Tomato-Masks/diy-fine-particulate-mask/designs/type-1/assets/CAD/misc/accordion-fold-diagram.png

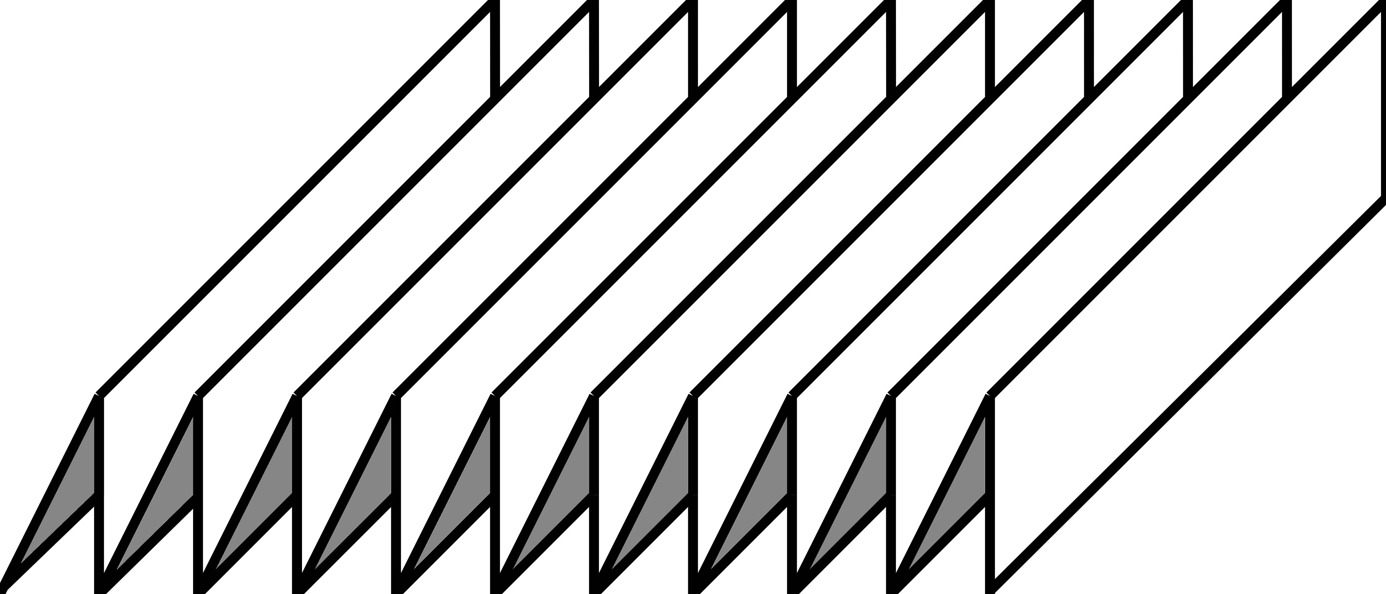
designs/type-1/assets/CAD/misc/accordion-fold-diagram.png
