Tomato-Masks/diy-fine-particulate-mask/designs/type-1/assets/CAD/misc/concept.png

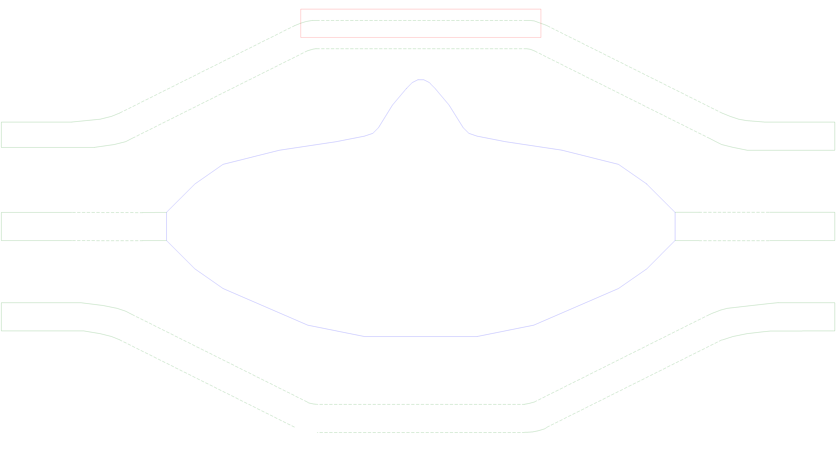
designs/type-1/assets/CAD/misc/concept.png
