Tomato-Masks/diy-fine-particulate-mask/designs/type-1/assets/images/inner-layer/design-sewed-edges-inner-layer-270by210.png

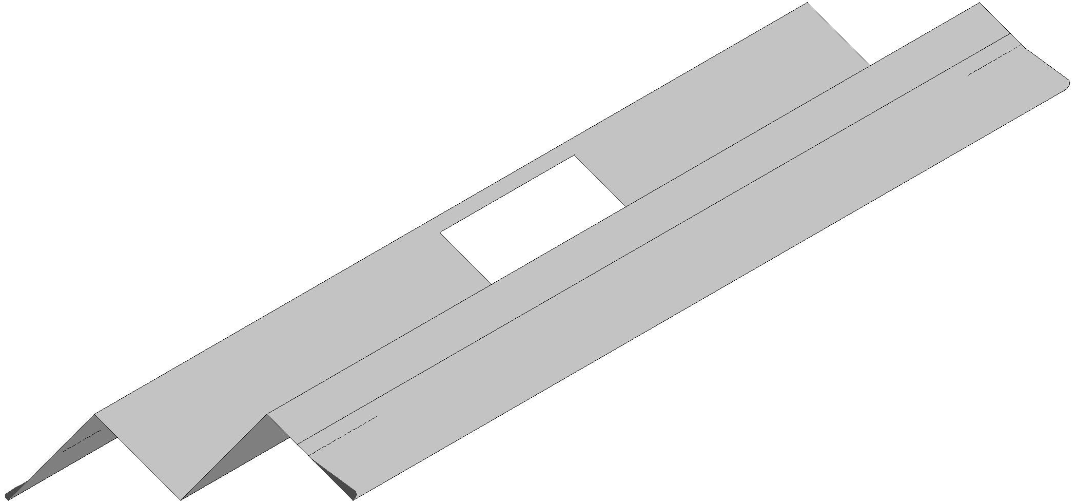
designs/type-1/assets/images/inner-layer/design-sewed-edges-inner-layer-270by210.png
