Tomato-Masks/diy-fine-particulate-mask/designs/type-1/assets/images/inner-layer/v04-inner-7.jpg

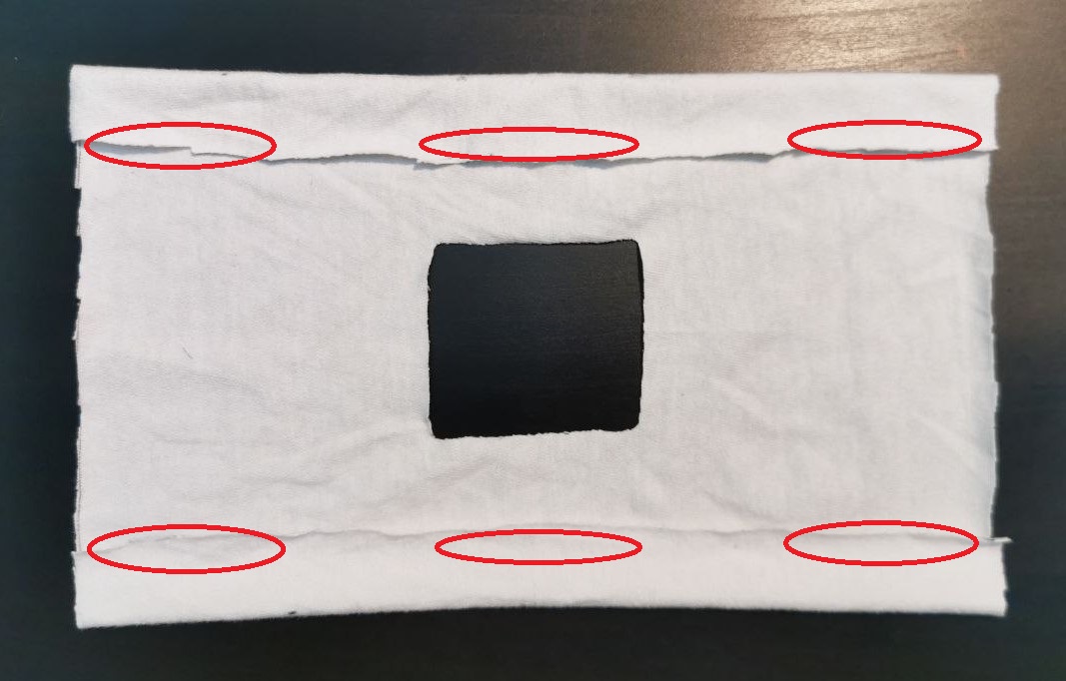
designs/type-1/assets/images/inner-layer/v04-inner-7.jpg
