Tomato-Masks/diy-fine-particulate-mask/designs/type-1/assets/images/misc/arch/inner-layer-labelled.png

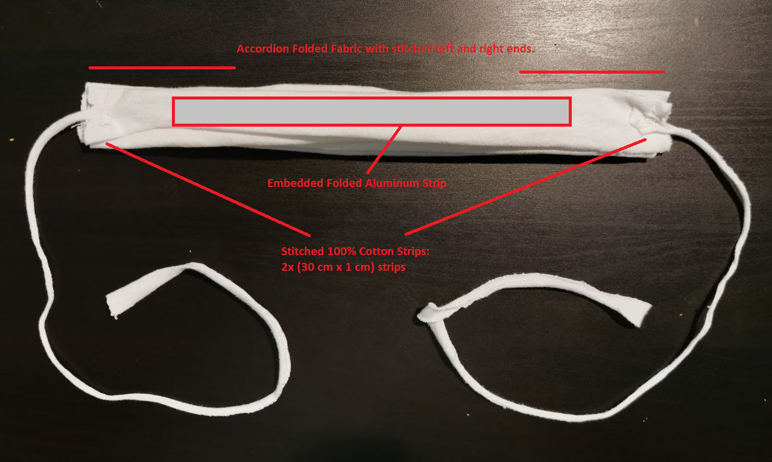
designs/type-1/assets/images/misc/arch/inner-layer-labelled.png
