Tomato-Masks/diy-fine-particulate-mask/designs/type-1/assets/images/misc/arch/inner-shell.jpg

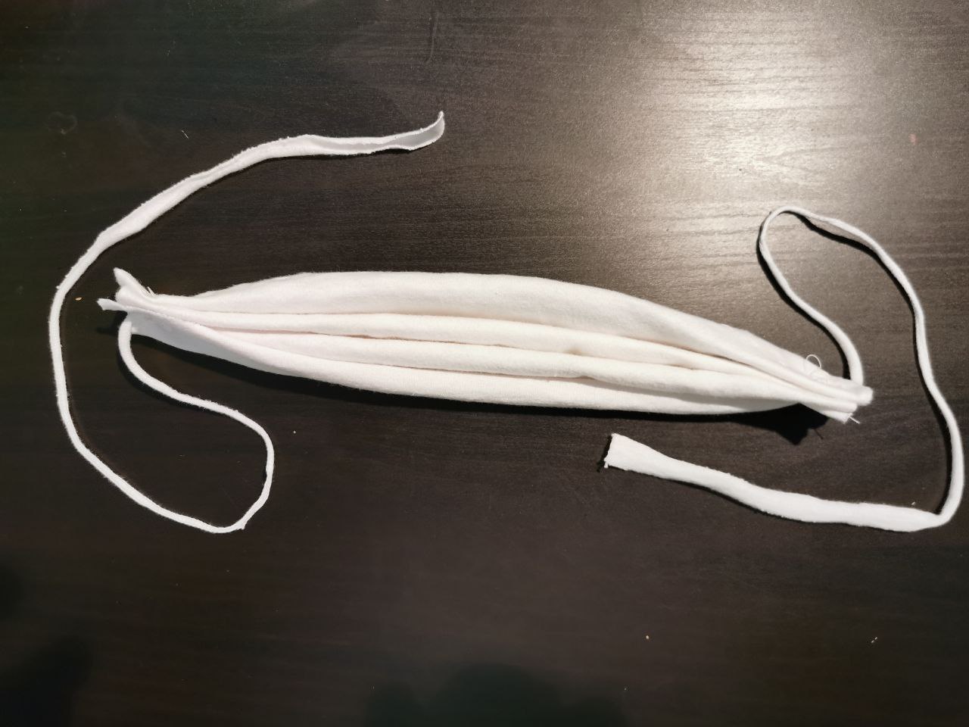
designs/type-1/assets/images/misc/arch/inner-shell.jpg
