Tomato-Masks/diy-fine-particulate-mask/designs/type-1/assets/images/misc/arch/rectangle.jpg

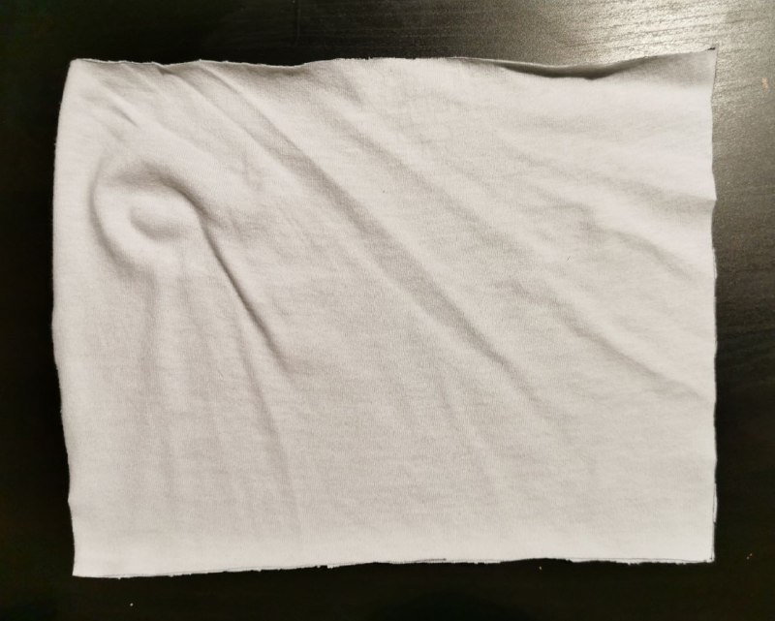
designs/type-1/assets/images/misc/arch/rectangle.jpg
