Tomato-Masks/diy-fine-particulate-mask/designs/type-1/assets/images/misc/arch/Small-Stencil-Outer-Layer.png

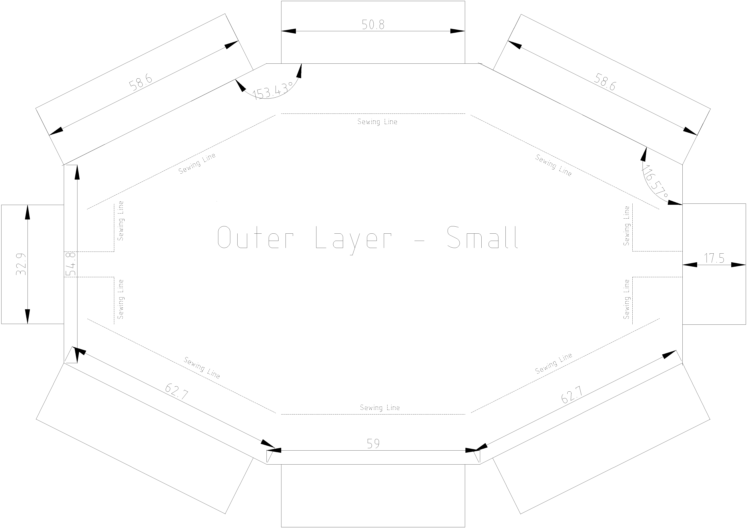
designs/type-1/assets/images/misc/arch/Small-Stencil-Outer-Layer.png
