Tomato-Masks/diy-fine-particulate-mask/designs/type-1/assets/images/misc/arch/v04-outer-layer.jpg

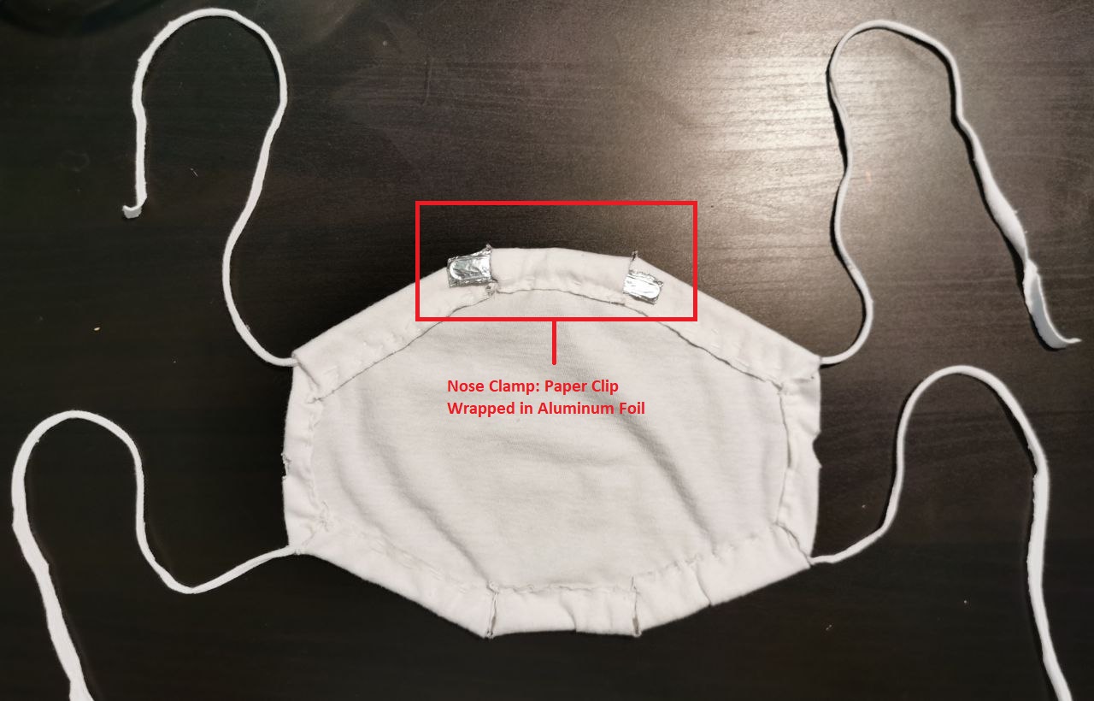
designs/type-1/assets/images/misc/arch/v04-outer-layer.jpg
