Tomato-Masks/diy-fine-particulate-mask/designs/type-1/assets/images/misc/inner-layer-fold.png

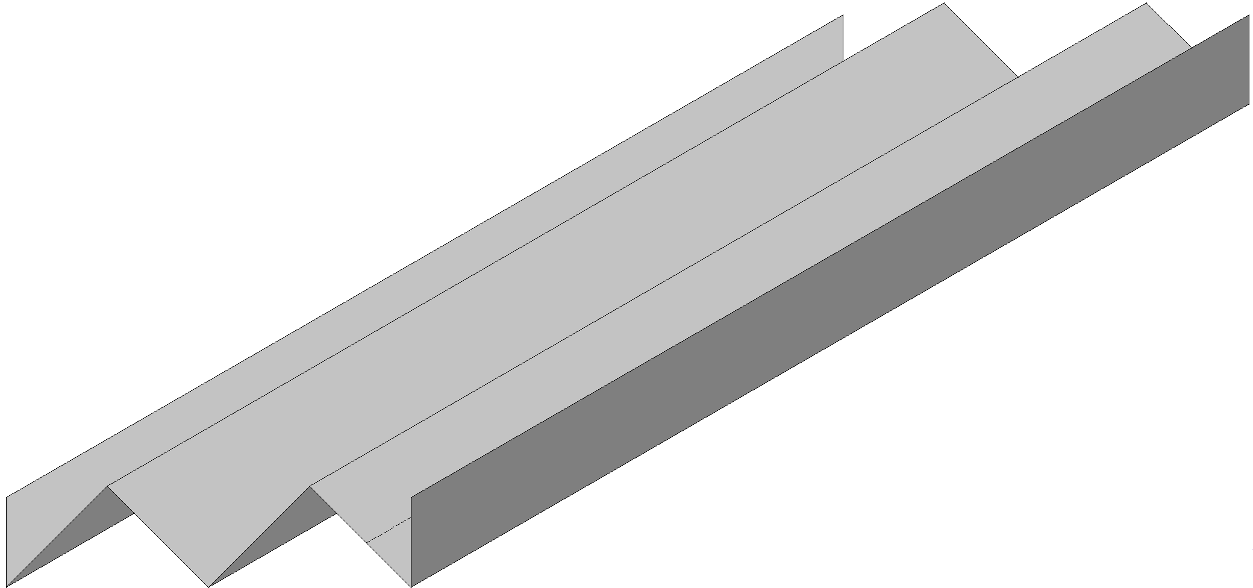
designs/type-1/assets/images/misc/inner-layer-fold.png
