Tomato-Masks/diy-fine-particulate-mask/designs/type-1/assets/images/misc/reference-inner-layer-270by210.png

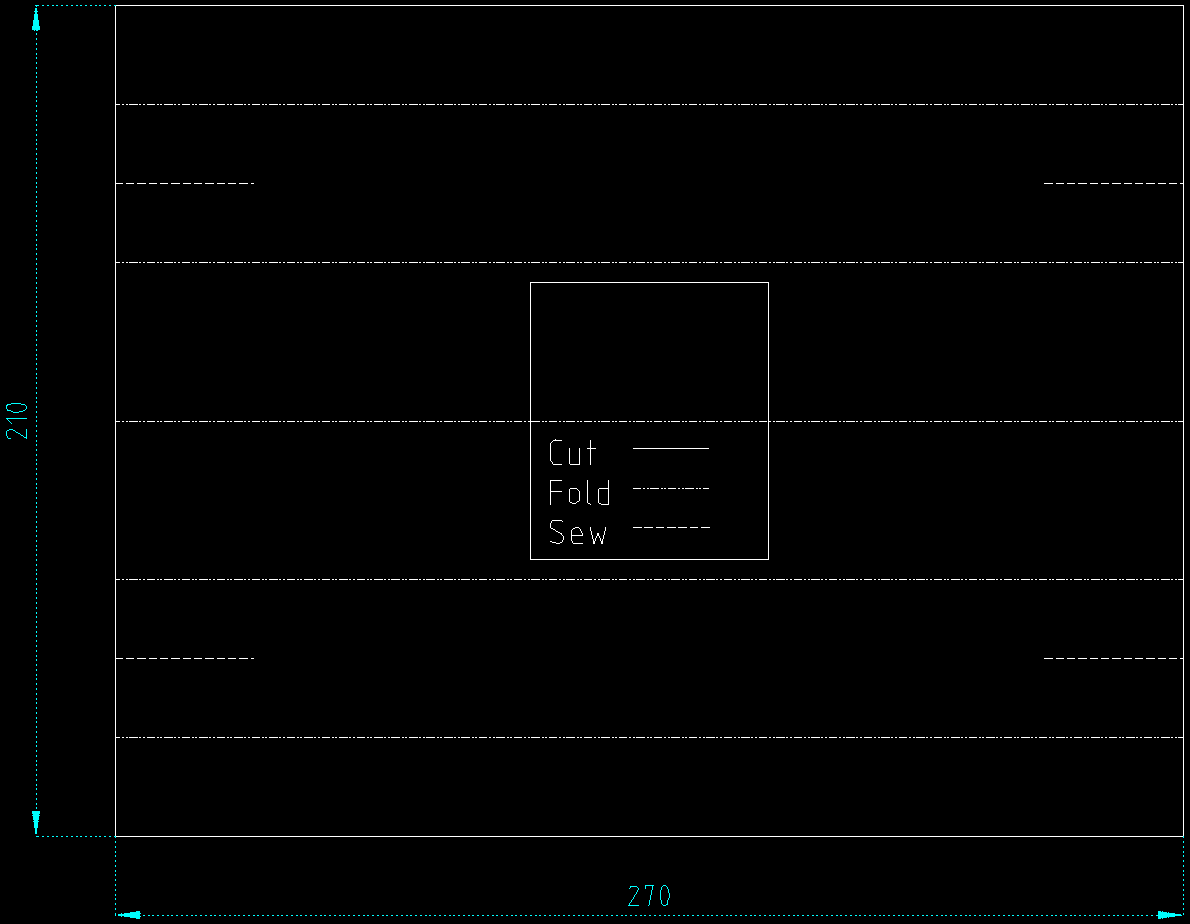
designs/type-1/assets/images/misc/reference-inner-layer-270by210.png
