Tomato-Masks/diy-fine-particulate-mask/designs/type-1/assets/images/misc/reference-outer-layer-270by200.png

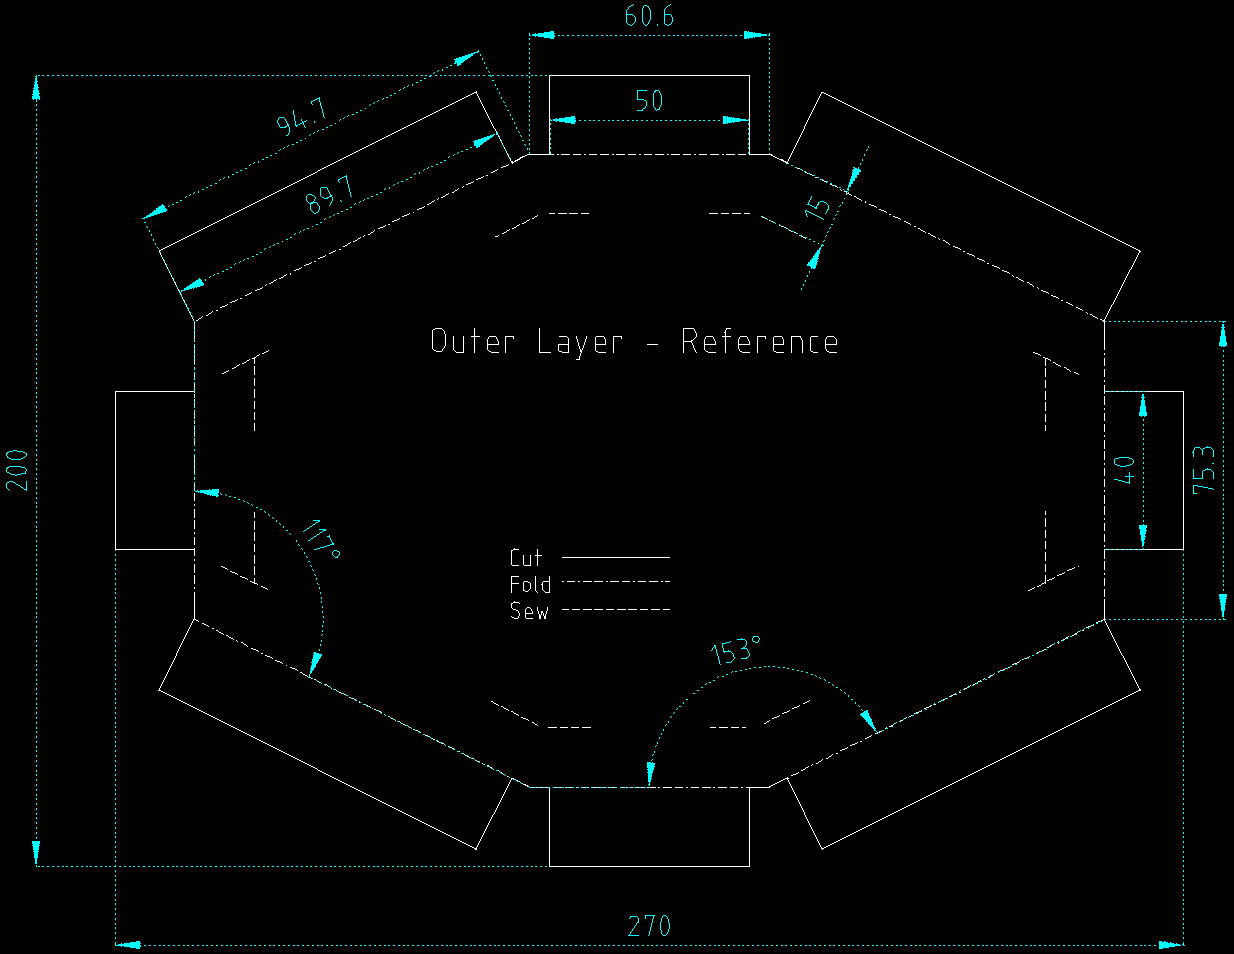
designs/type-1/assets/images/misc/reference-outer-layer-270by200.png
