Tomato-Masks/diy-fine-particulate-mask/designs/type-1/assets/images/misc/v04-inner-10.jpg

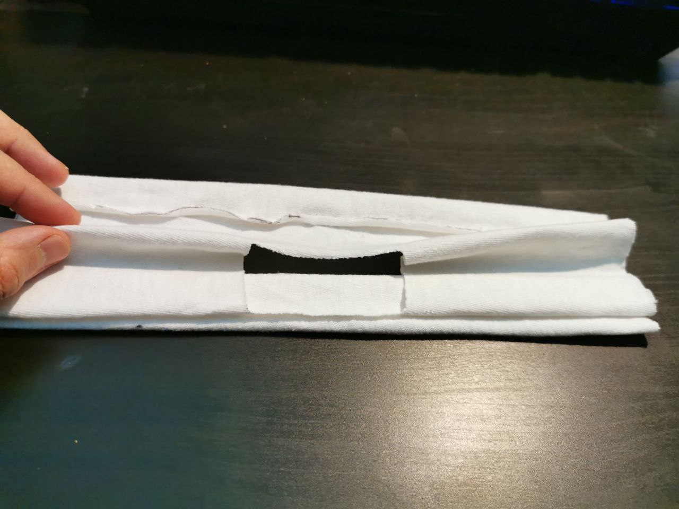
designs/type-1/assets/images/misc/v04-inner-10.jpg
