Tomato-Masks/diy-fine-particulate-mask/designs/type-1/assets/images/misc/v04-inner-12.jpg

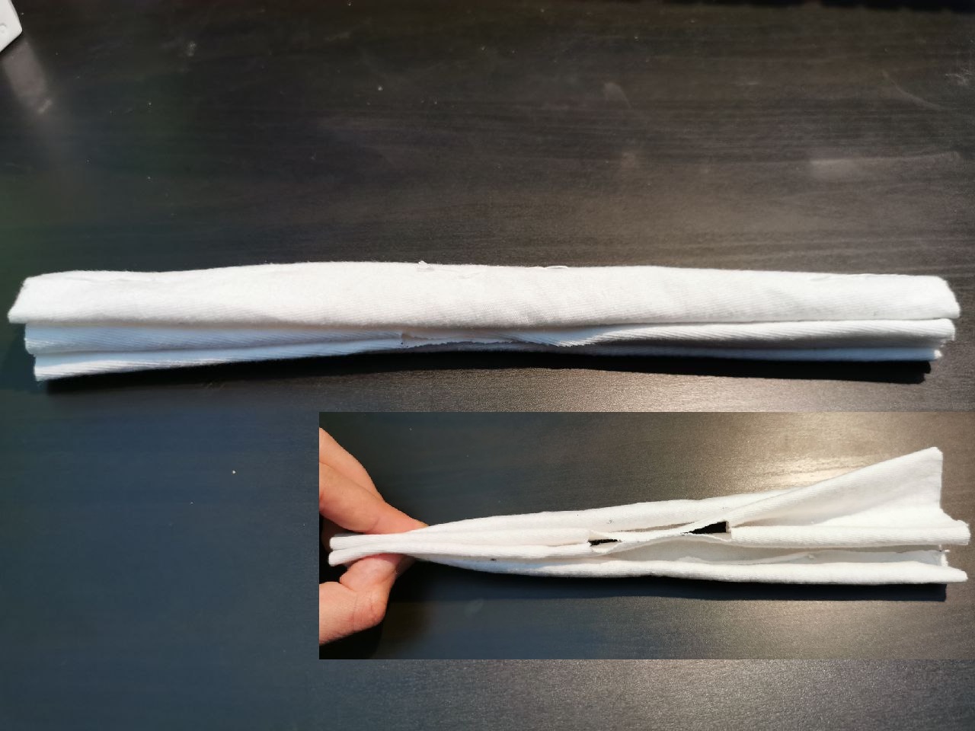
designs/type-1/assets/images/misc/v04-inner-12.jpg
