Tomato-Masks/diy-fine-particulate-mask/designs/type-1/assets/images/preparation/fabric-stripes.jpg

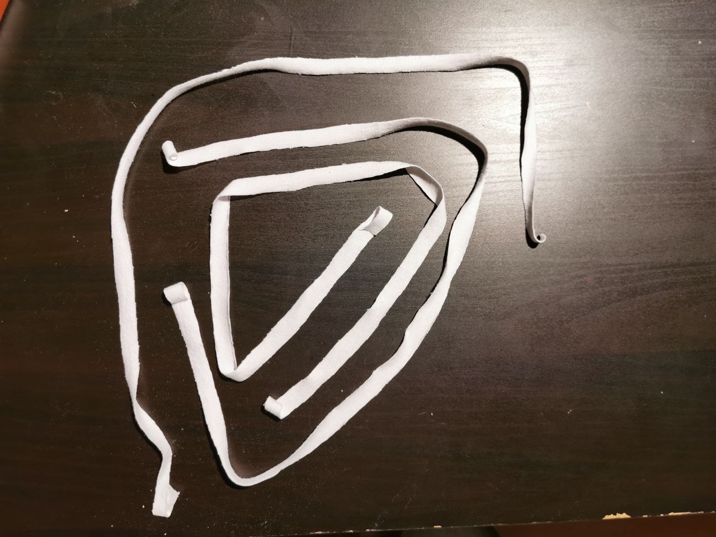
designs/type-1/assets/images/preparation/fabric-stripes.jpg
