Tomato-Masks/diy-fine-particulate-mask/designs/type-1/assets/images/preparation/roll-paper-stripe.jpg

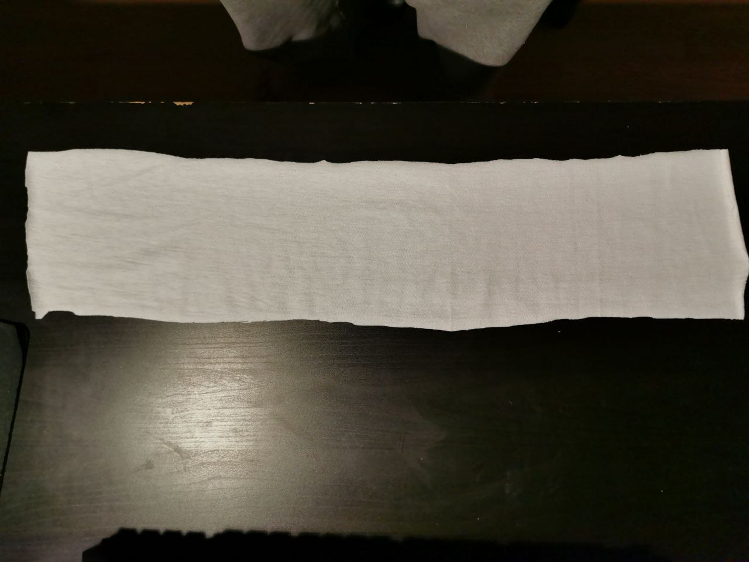
designs/type-1/assets/images/preparation/roll-paper-stripe.jpg
