Tomato-Masks/diy-fine-particulate-mask/designs/type-1/assets/images/preparation/stripe-roll.jpg

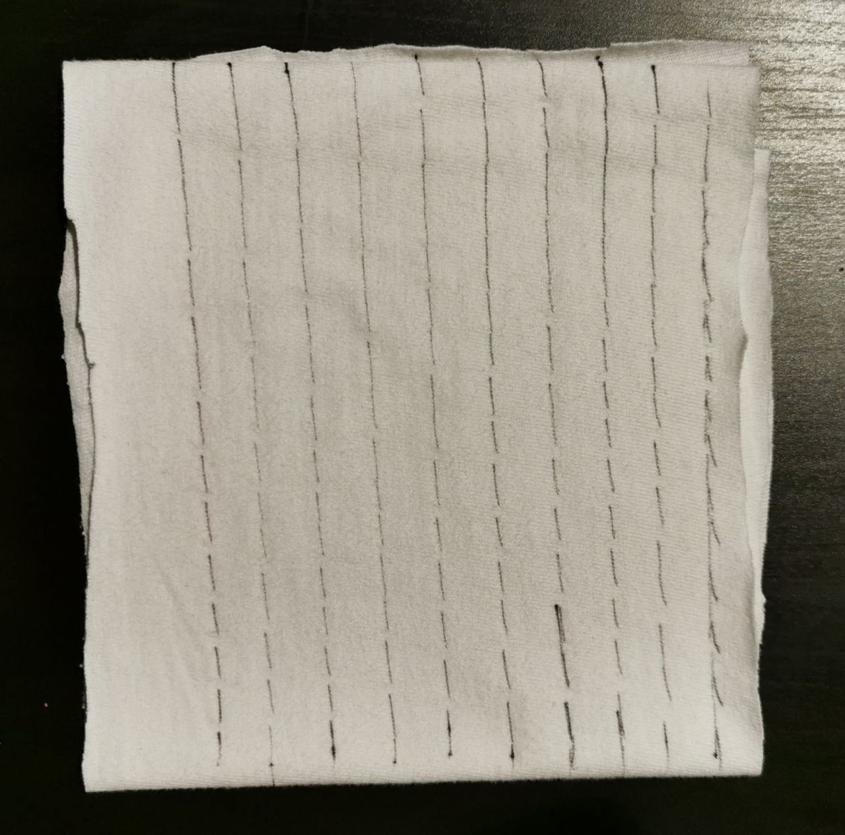
designs/type-1/assets/images/preparation/stripe-roll.jpg
