Tomato-Masks/diy-fine-particulate-mask/designs/type-1/assets/images/type1v04/fitting-v04-2b.jpg

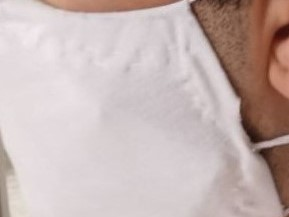
designs/type-1/assets/images/type1v04/fitting-v04-2b.jpg
