Tomato-Masks/diy-fine-particulate-mask/designs/type-1/assets/images/type1v04/v04-12b.jpg

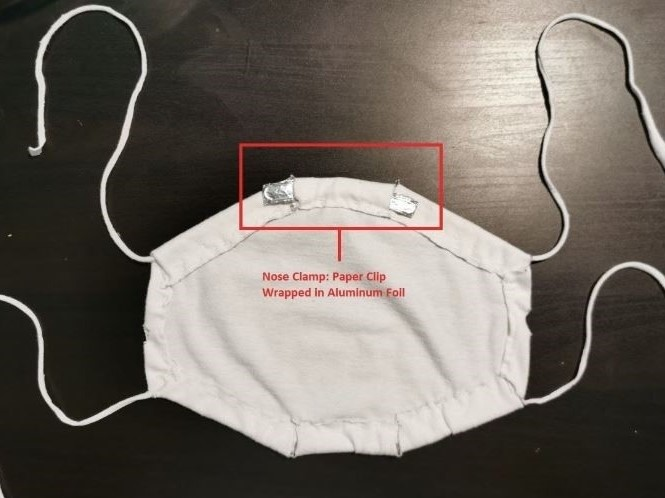
designs/type-1/assets/images/type1v04/v04-12b.jpg
