Tomato-Masks/diy-fine-particulate-mask/designs/type-1/assets/images/misc/inner-layer-fabric-guide.png

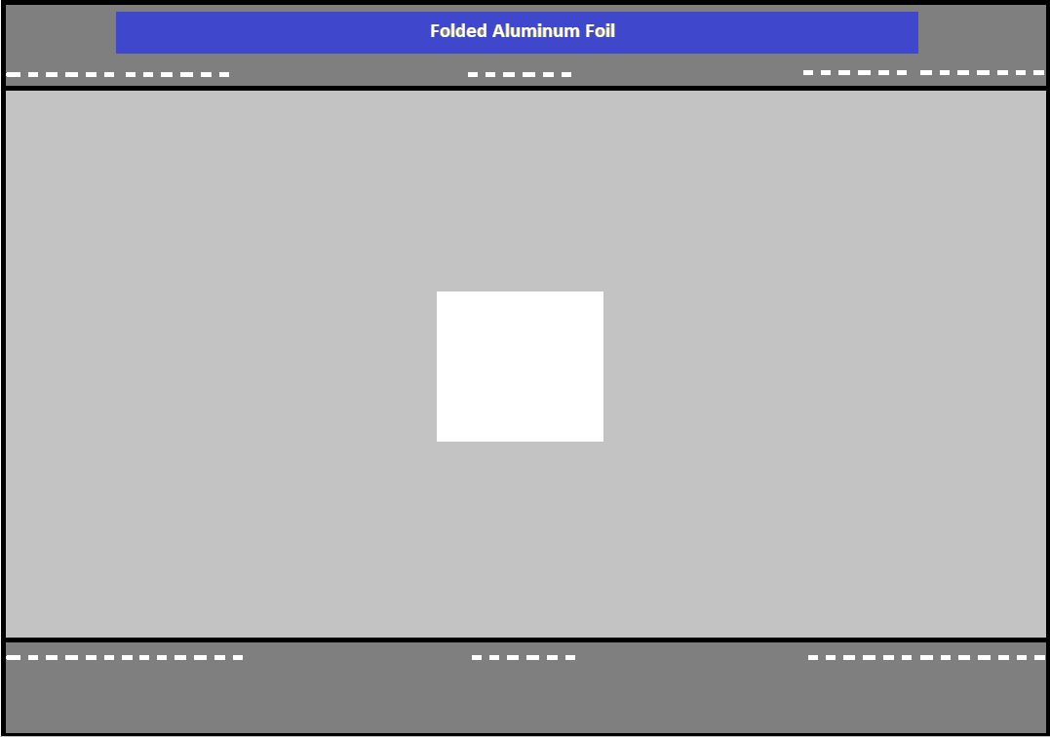
designs/type-1/assets/images/misc/inner-layer-fabric-guide.png
