Tomato-Masks/diy-fine-particulate-mask/designs/type-1/assets/images/misc/inner-layer-instructions.jpg

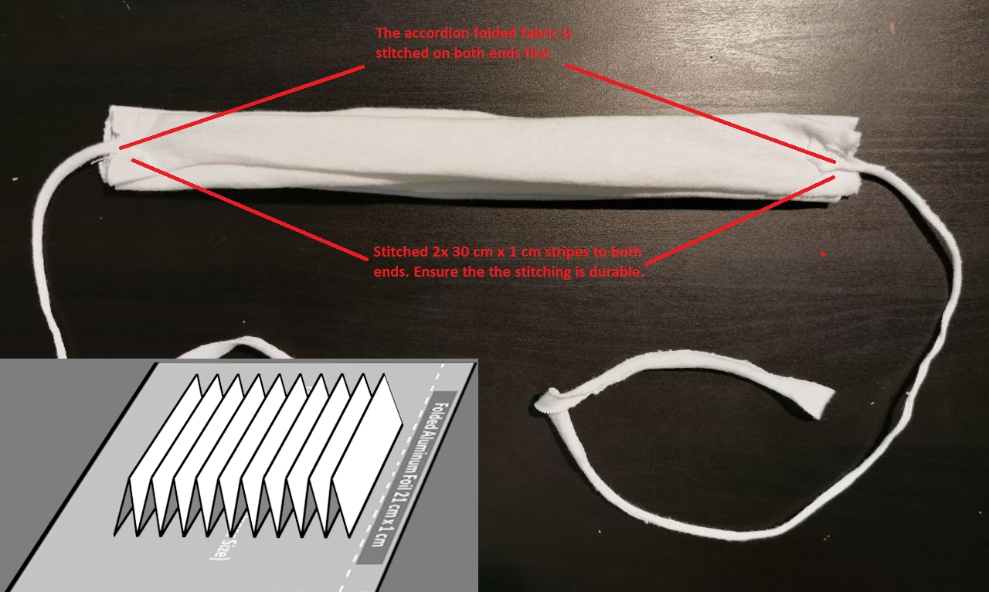
designs/type-1/assets/images/misc/inner-layer-instructions.jpg
